AndresRicoM/axol/homehub/board_fab/bucket_sleep_outline.png

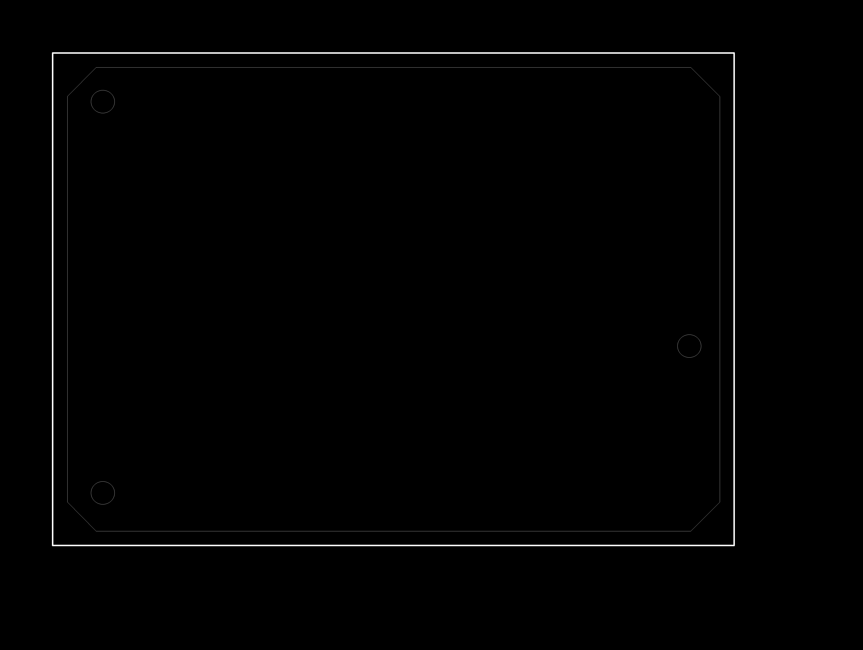
homehub/board_fab/bucket_sleep_outline.png
