AndresRicoM/axol/homehub/board_fab/bucket_sleep_outline_in.png

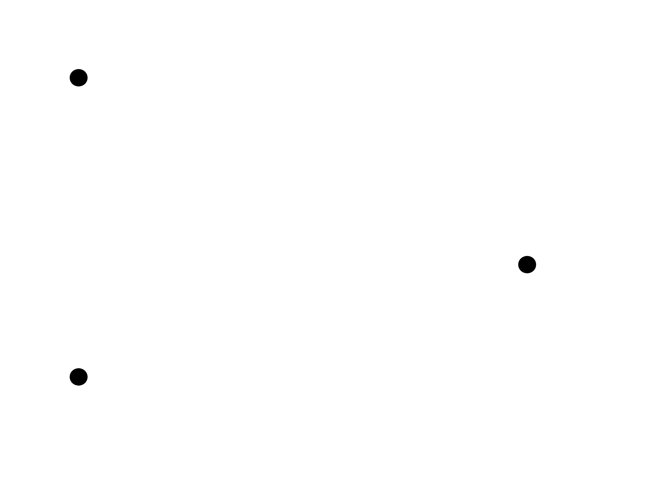
homehub/board_fab/bucket_sleep_outline_in.png
