AndresRicoM/axol/homehub/board_fab/bucket_sleep_outline_out.png

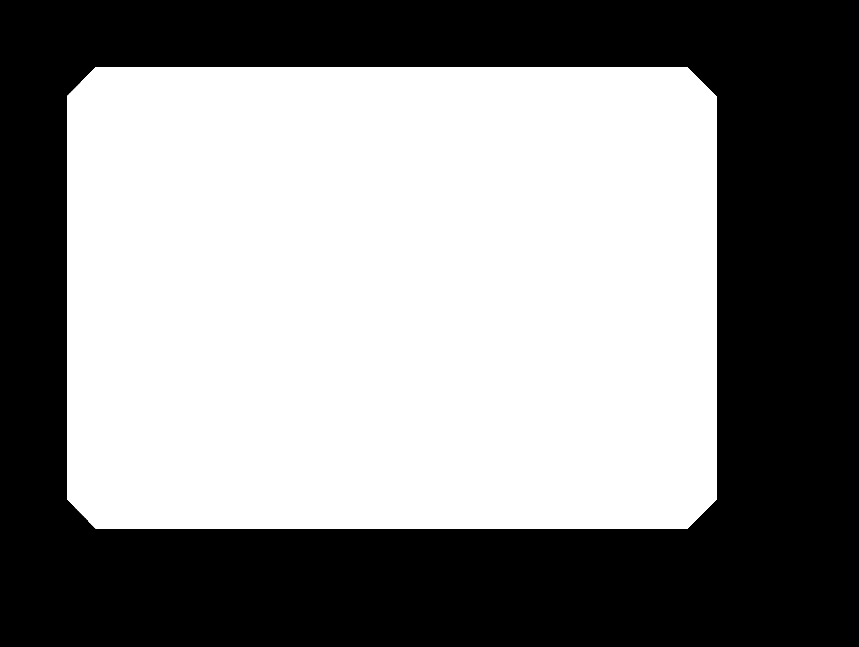
homehub/board_fab/bucket_sleep_outline_out.png
