AndresRicoM/axol/homehub/board_fab/bucket_sleep_traces.png

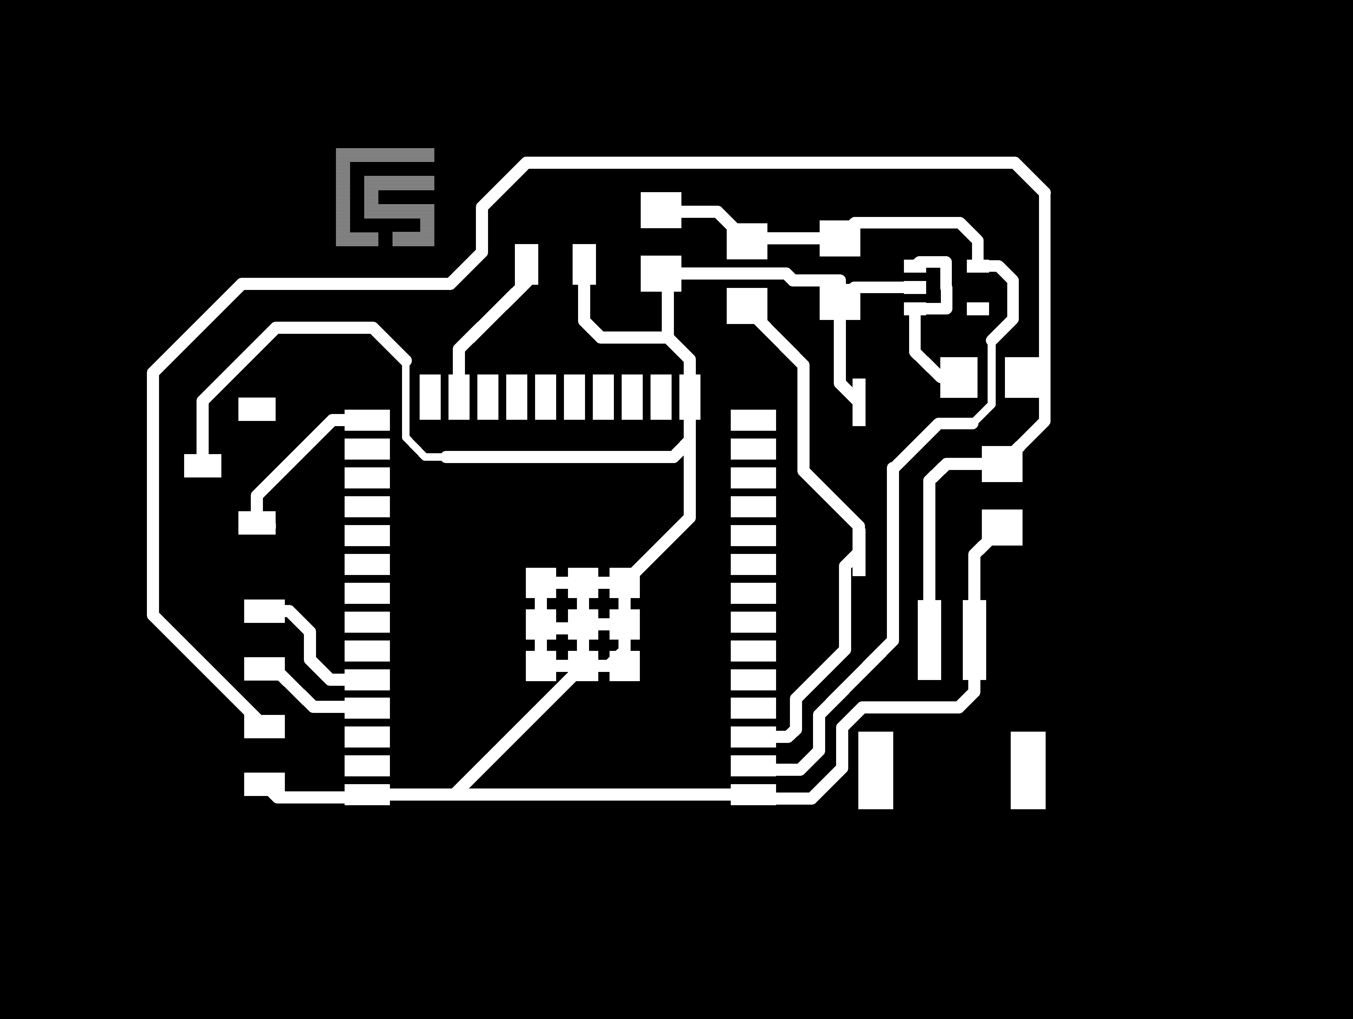
homehub/board_fab/bucket_sleep_traces.png
