AndresRicoM/axol/images/env_diagram.jpeg

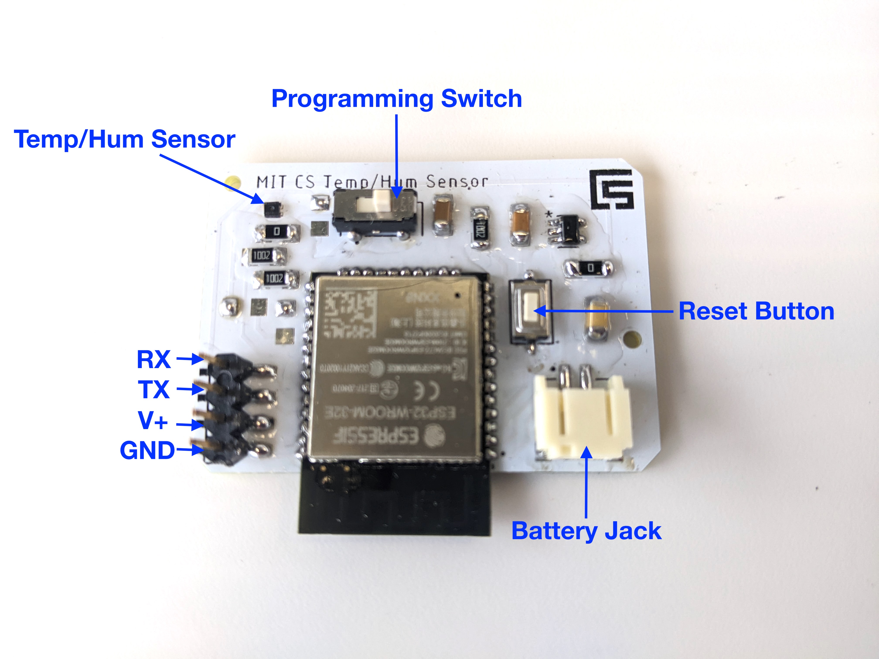
images/env_diagram.jpeg
