AndresRicoM/axol/sensors/environmental_sensor/board_fab/environment_traces.png

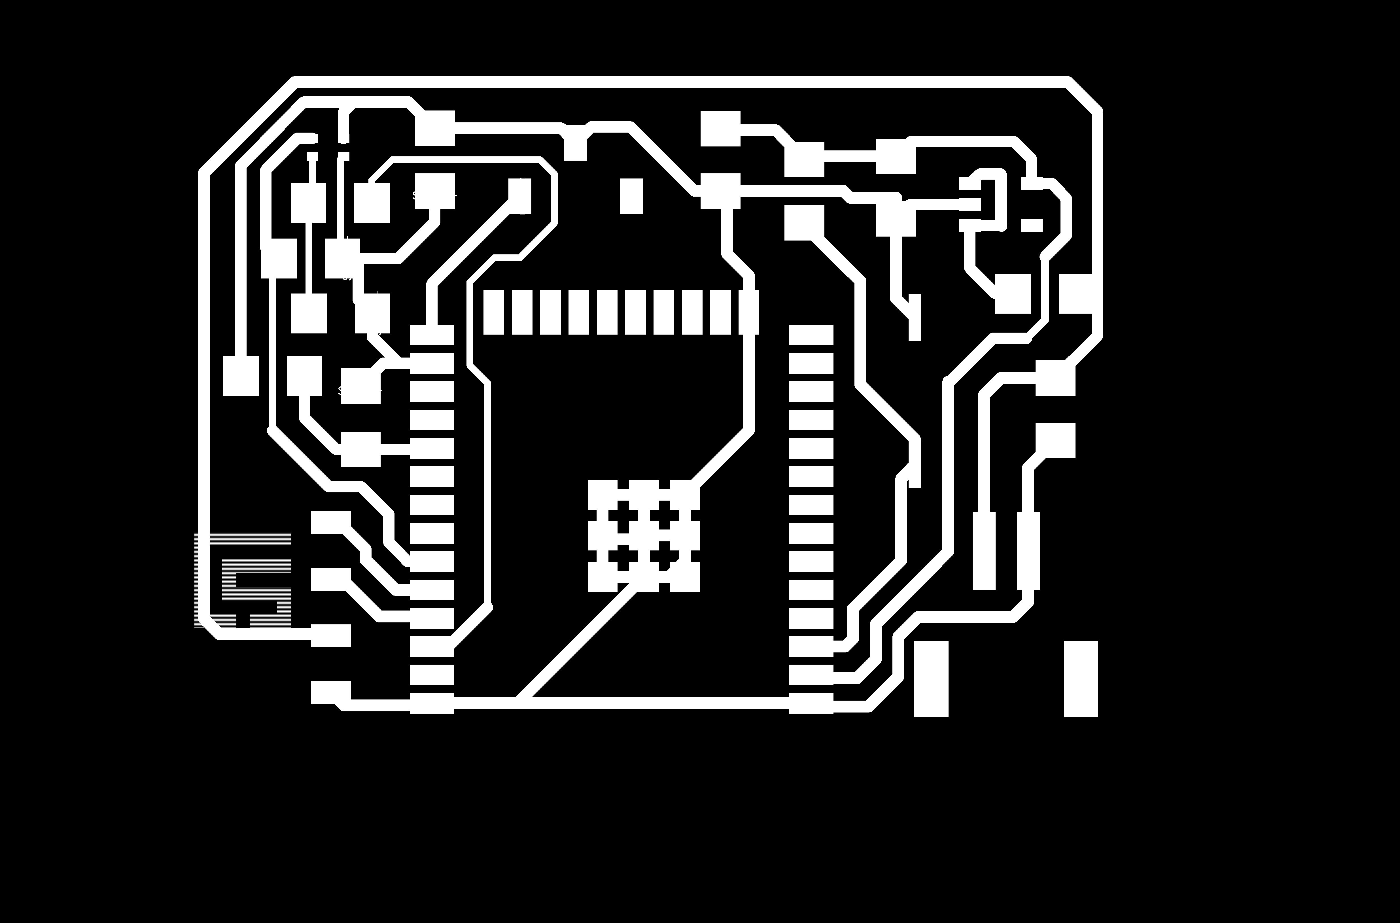
sensors/environmental_sensor/board_fab/environment_traces.png
