AndresRicoM/axol/sensors/environmental_sensor/board_fab/environmental_outline_out.png

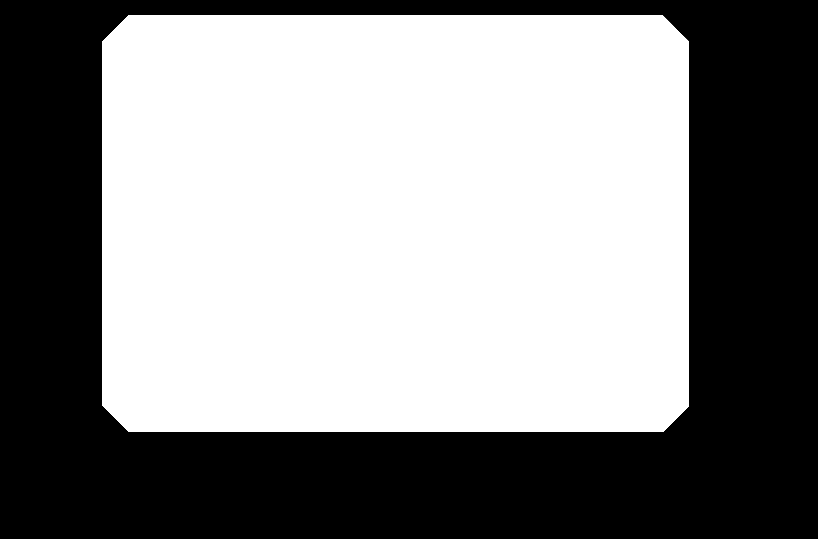
sensors/environmental_sensor/board_fab/environmental_outline_out.png
