AndresRicoM/axol/sensors/tank_sensor/board_fab/tank_outline.png

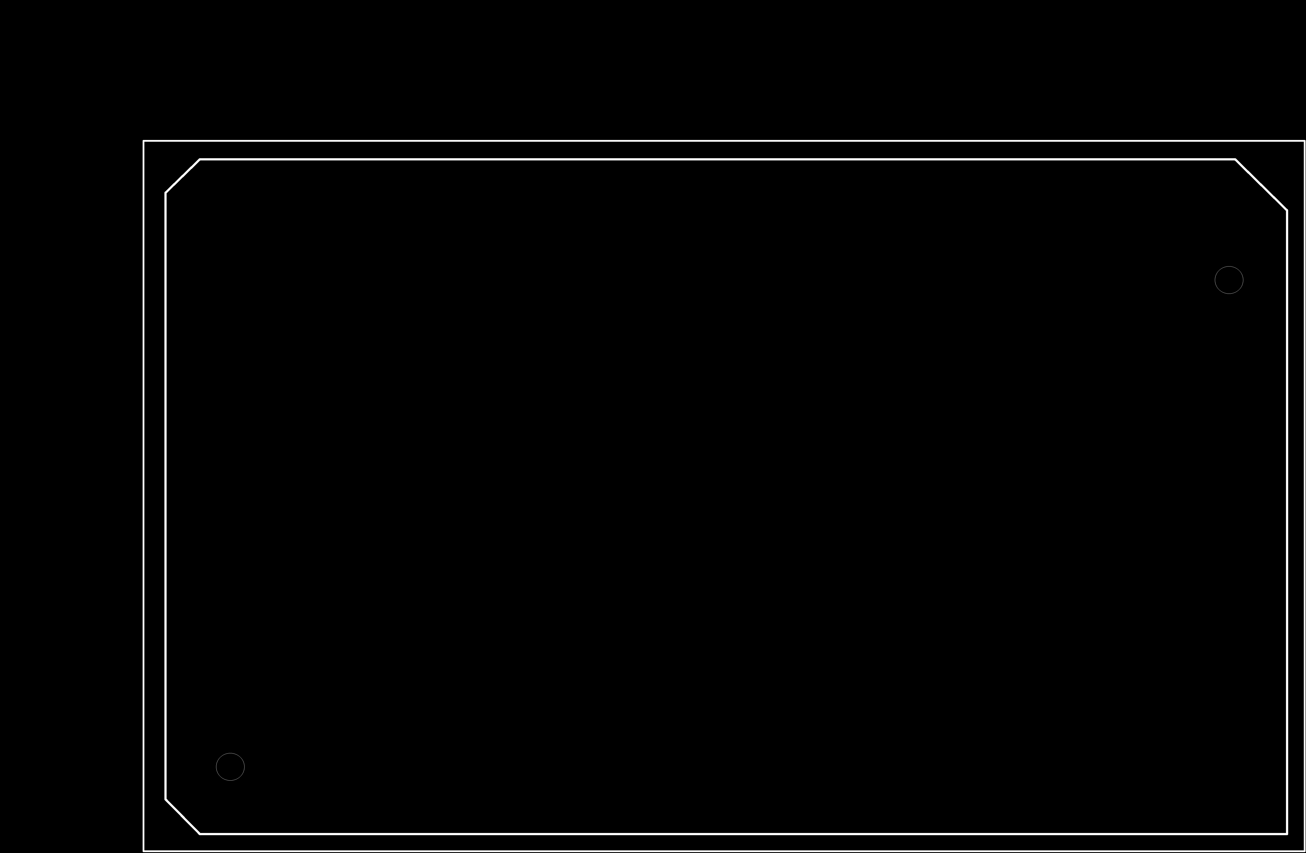
sensors/tank_sensor/board_fab/tank_outline.png
