AndresRicoM/axol/sensors/tank_sensor/board_fab/tank_outline_out.png

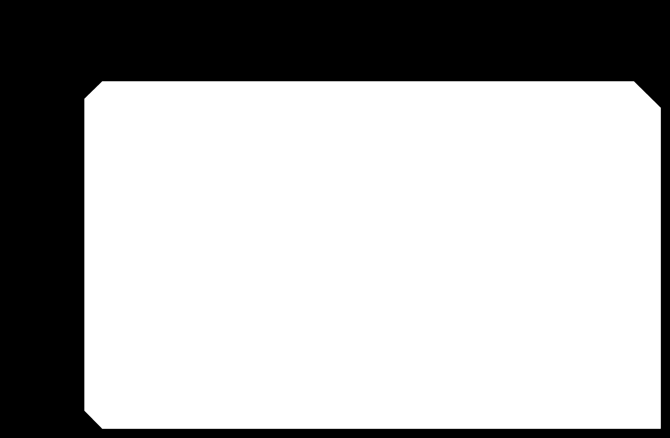
sensors/tank_sensor/board_fab/tank_outline_out.png
