AndresRicoM/axol/sensors/tank_sensor/board_fab/tank_traces.png

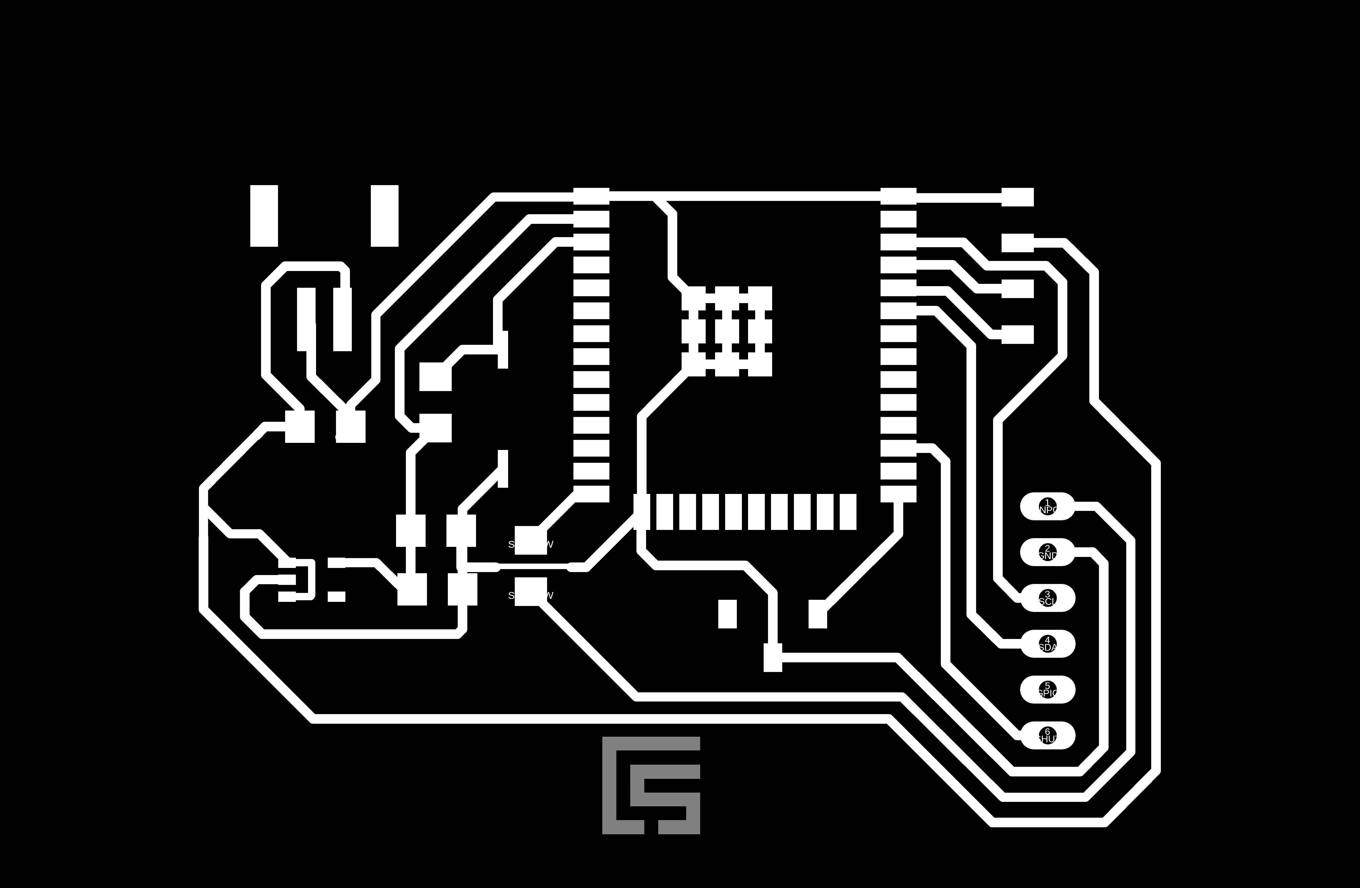
sensors/tank_sensor/board_fab/tank_traces.png
