AndresRicoM/axol/sensors/water_quality_sensor/board_fab/quality_traces.png

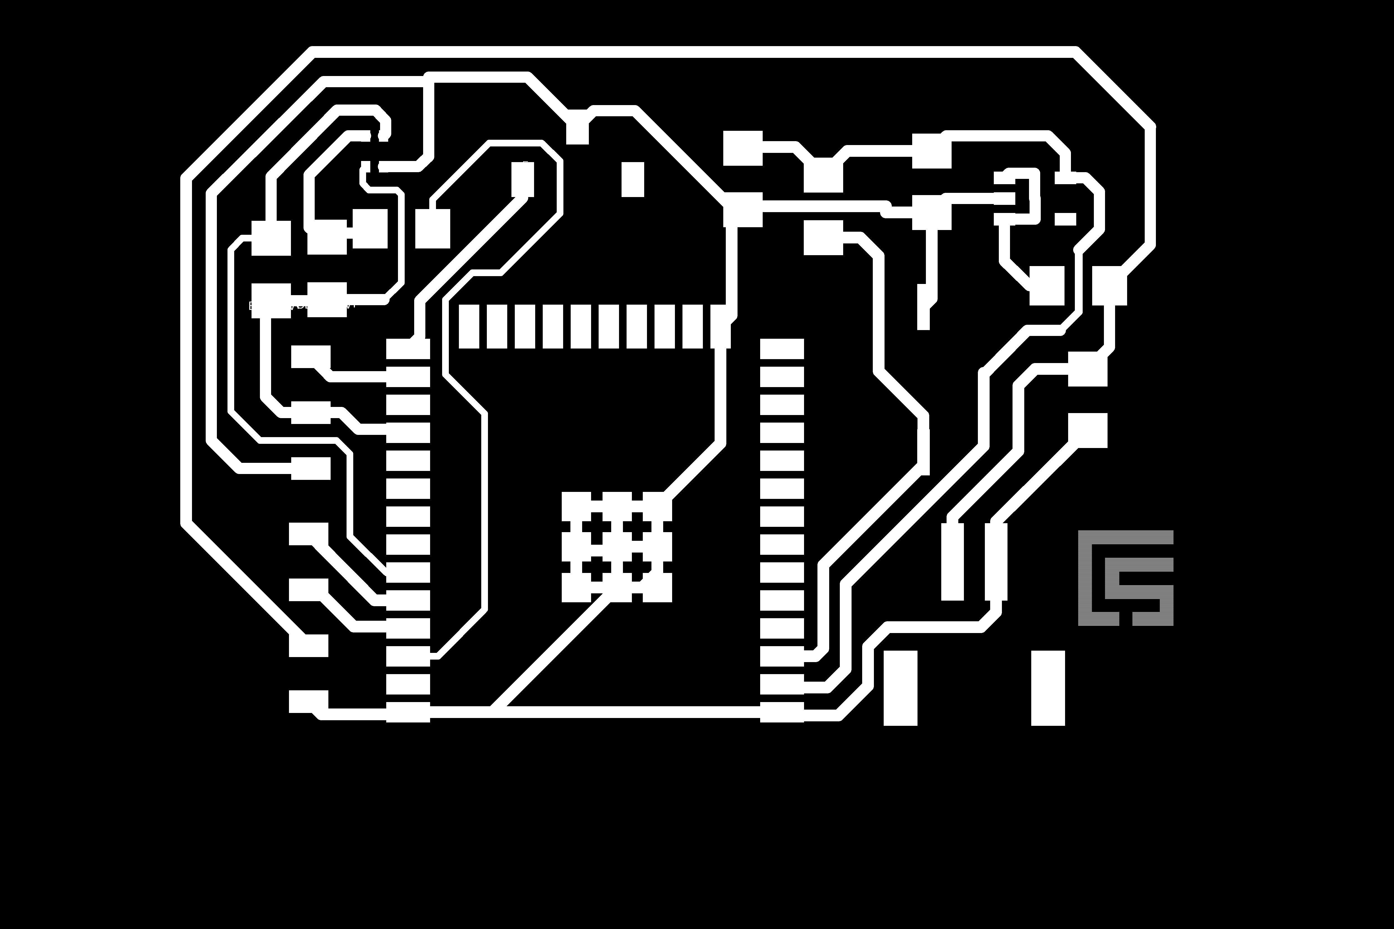
sensors/water_quality_sensor/board_fab/quality_traces.png
