AndresRicoM/axol/sensors/water_quality_sensor/case/buoy_air_cavity.stl

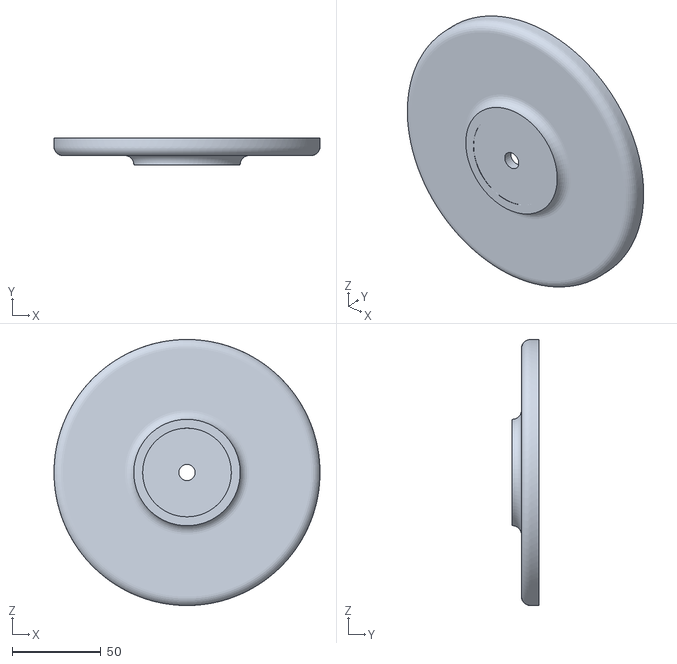
[picture p52: CAD file, 2023-02-08]
sensors/water_quality_sensor/case/buoy_air_cavity.stl
150.0 x 15.0 x 150.0
