AndresRicoM/axol/homehub/case/hh_lid.stl

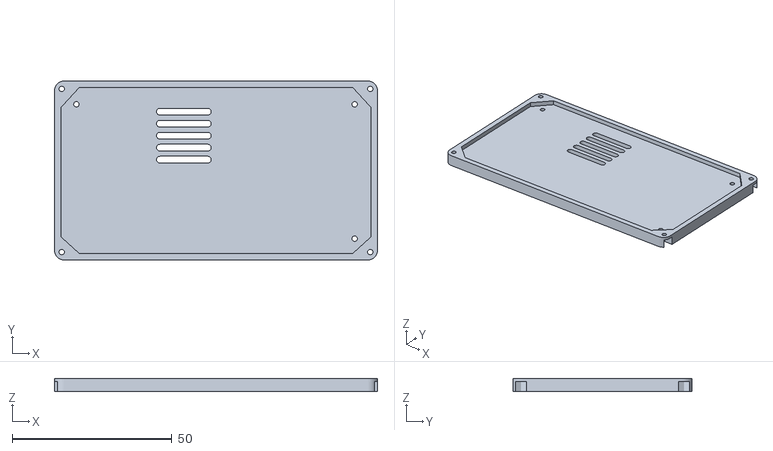
[picture p53: CAD file, 2023-01-26]
homehub/case/hh_lid.stl
101.0 x 56.0 x 4.10
