AndresRicoM/axol/sensors/water_quality_sensor/case/buoy_lid.dxf

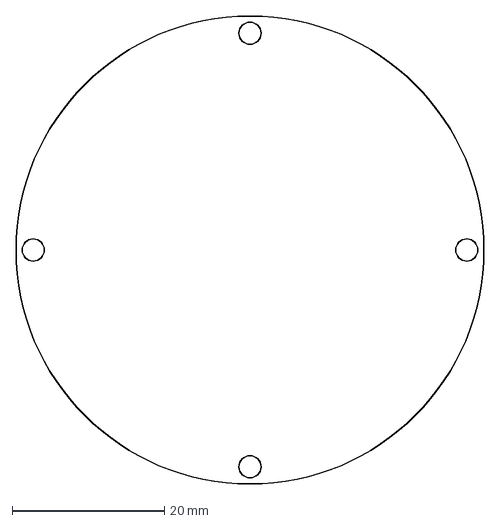
[picture p54: CAD file, 2023-02-08]
sensors/water_quality_sensor/case/buoy_lid.dxf
61.5 x 61.5 mm
