AndresRicoM/axol/sensors/water_quality_sensor/case/buoy_balast.stl

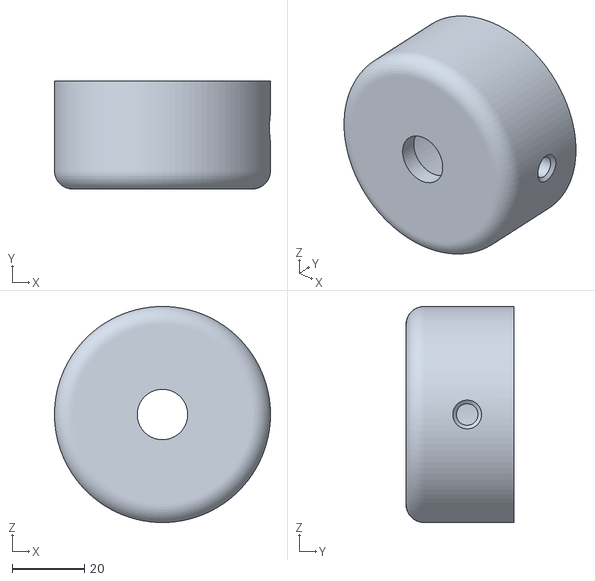
[picture p55: CAD file, 2023-02-08]
sensors/water_quality_sensor/case/buoy_balast.stl
60.0 x 30.0 x 60.0
